Coturex/Wifi_Mqtt_SmartMeter/test/led_blink_D5.cpp

#include <Arduino.h>

const int ledPin = D5;

void setup() {
  Serial.begin(115200);
  // setup pin 5 as a digital output pin
  pinMode (ledPin, OUTPUT);
}

void loop() {
  digitalWrite (ledPin, HIGH);	// turn on the LED

  delay(500);	// wait for half a second or 500 milliseconds

  digitalWrite (ledPin, LOW);	// turn off the LED

  delay(500);	// wait for half a second or 500 milliseconds
}
